medicationforall/dollhouse/doc_image/01.png

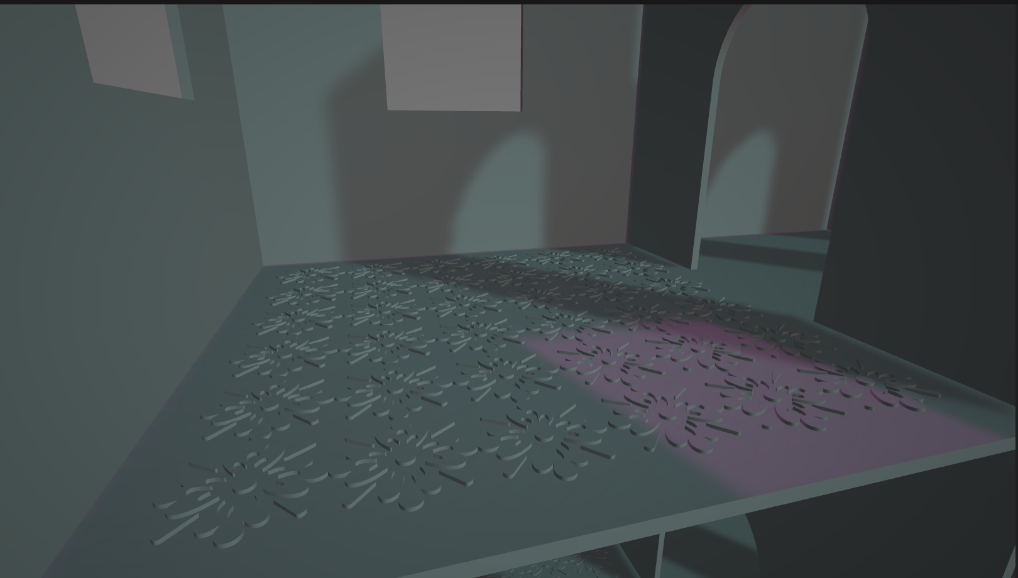
doc_image/01.png
