medicationforall/dollhouse/doc_image/02.png

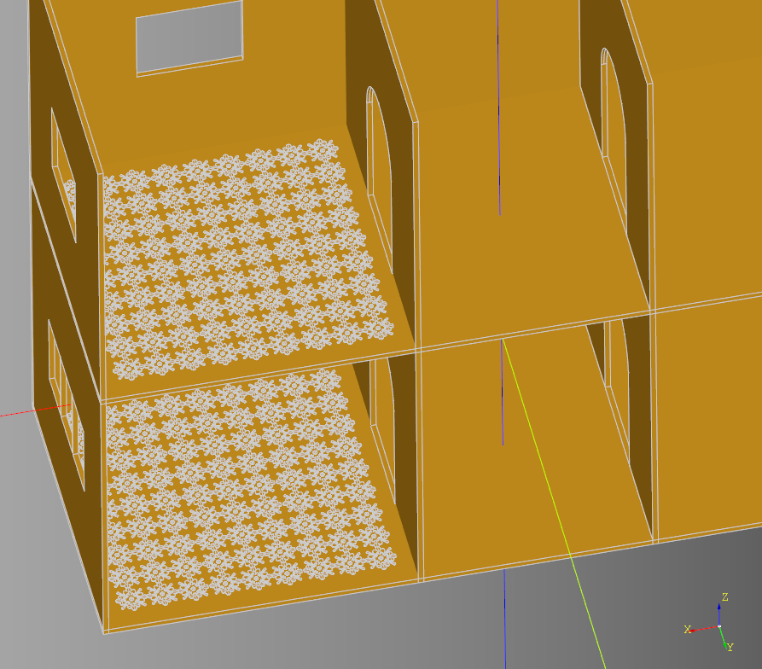
doc_image/02.png
