medicationforall/dollhouse/doc_image/09.png

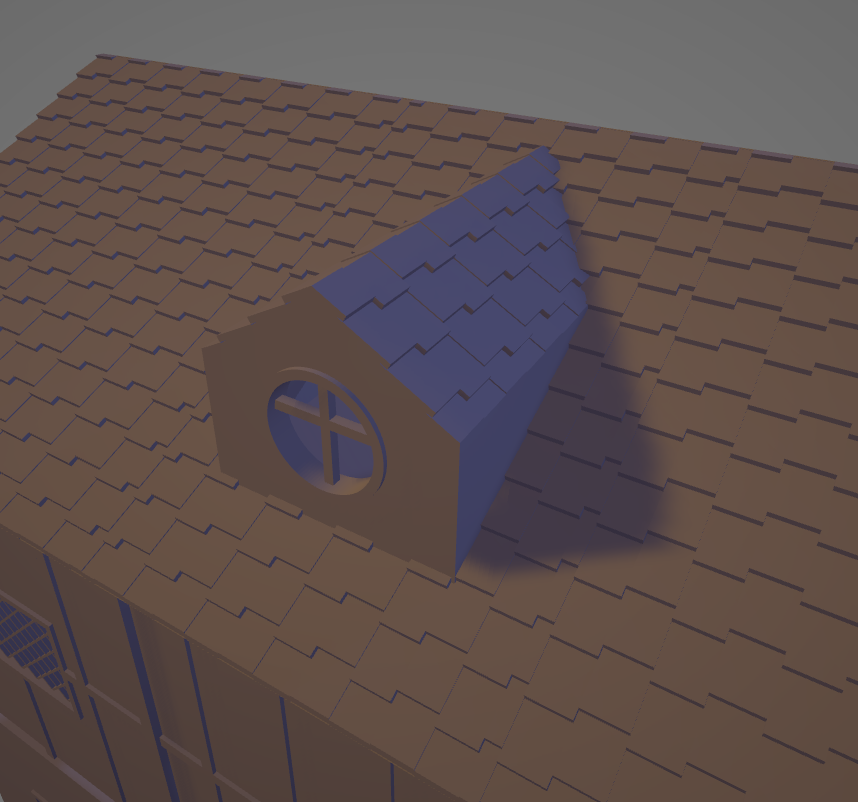
doc_image/09.png
