medicationforall/dollhouse/doc_image/10.png

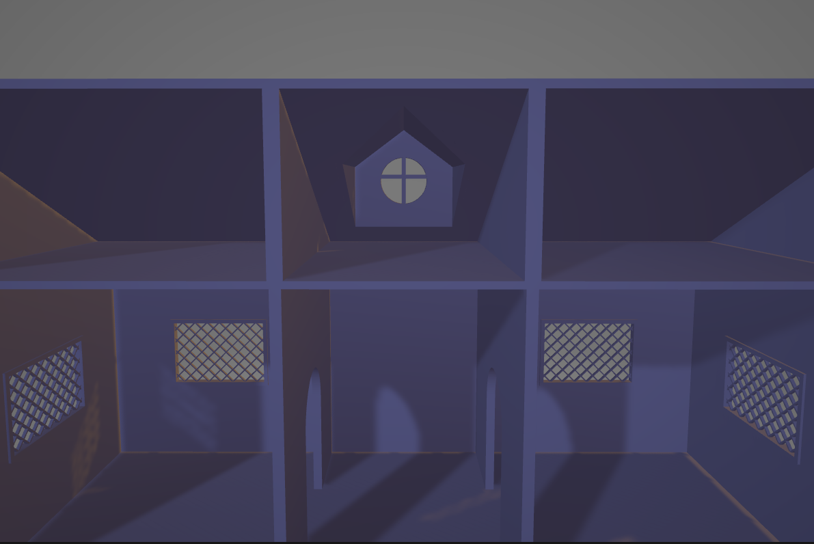
doc_image/10.png
