medicationforall/dollhouse/doc_image/11.png

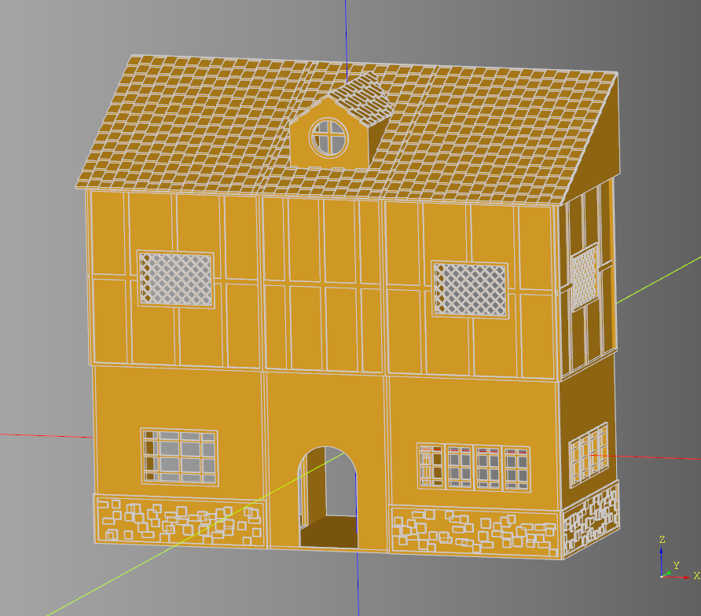
doc_image/11.png
