medicationforall/dollhouse/doc_image/12.png

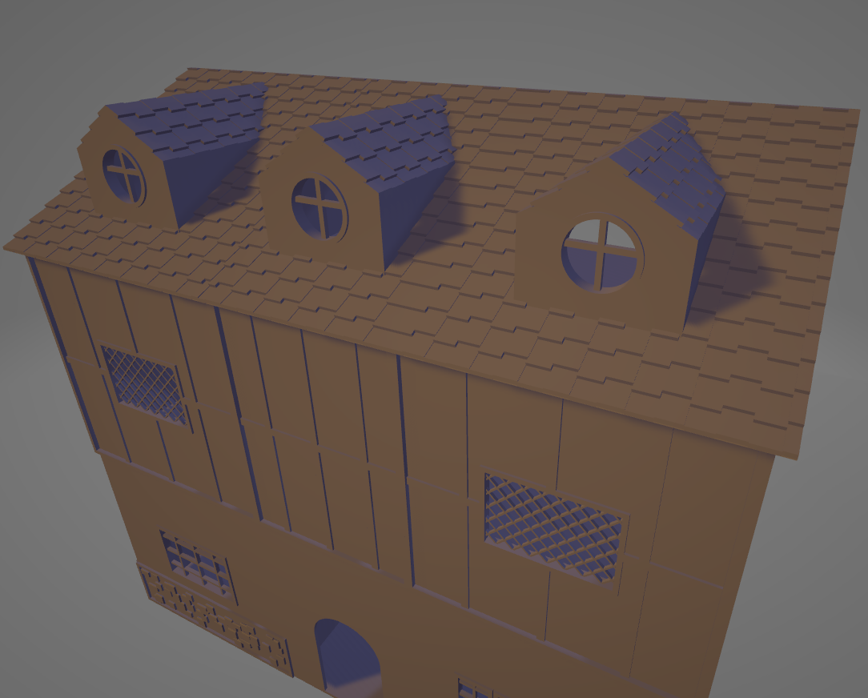
doc_image/12.png
