medicationforall/dollhouse/doc_image/13.png

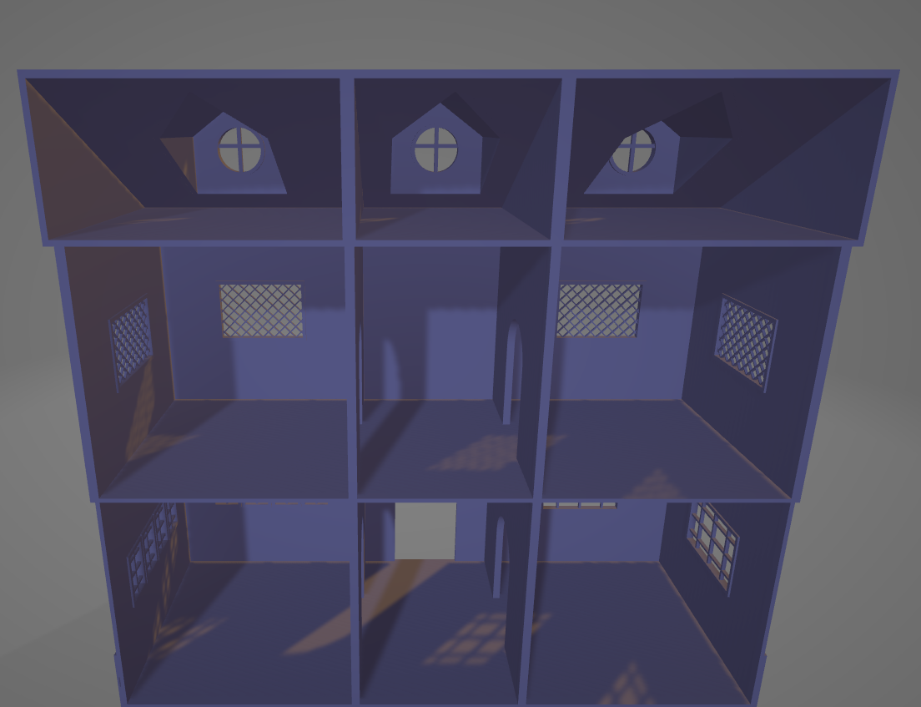
doc_image/13.png
