medicationforall/dollhouse/doc_image/14.png

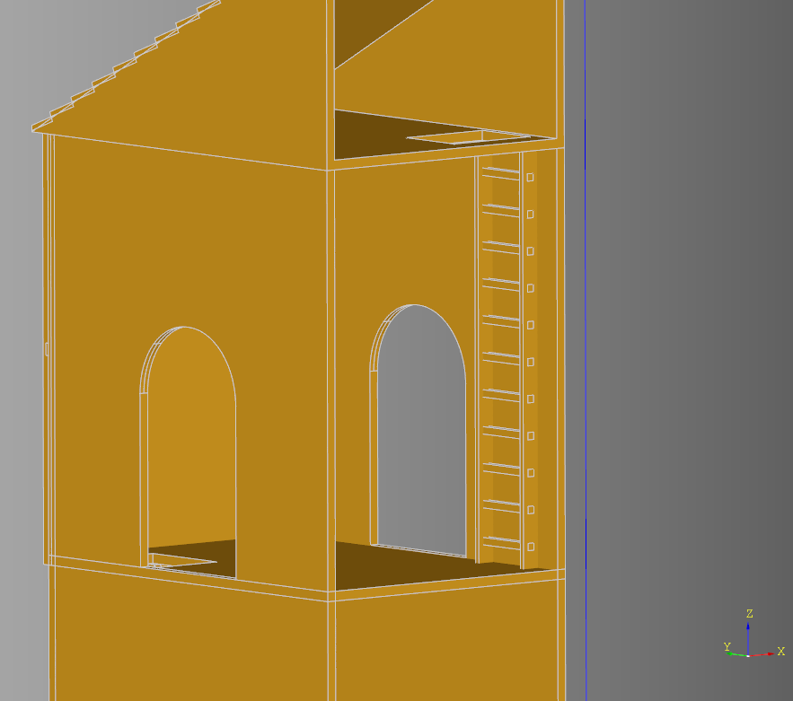
doc_image/14.png
