medicationforall/dollhouse/doc_image/15.png

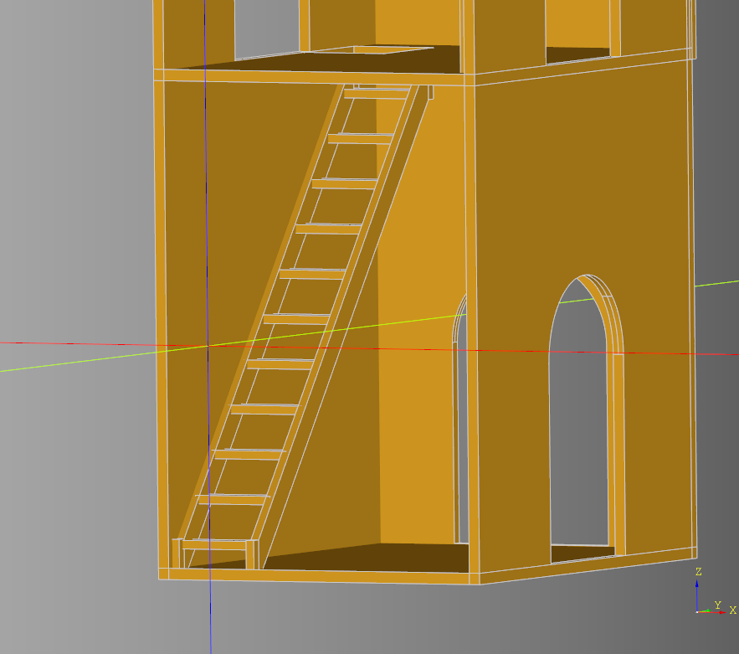
doc_image/15.png
