medicationforall/dollhouse/doc_image/17.png

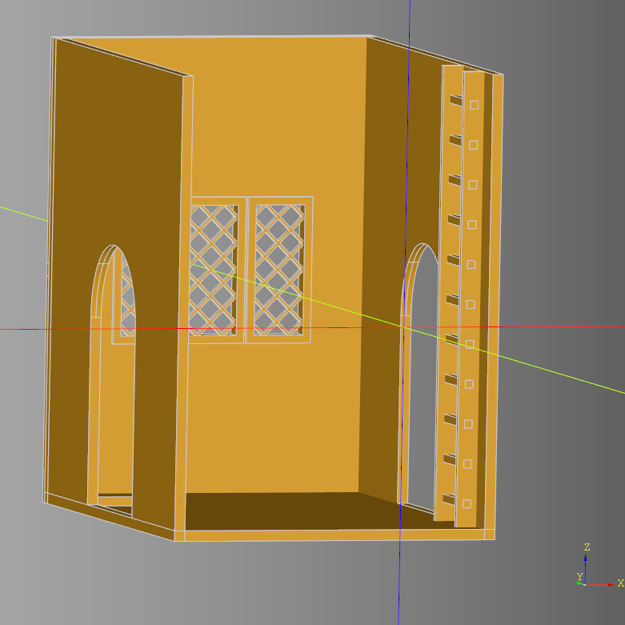
doc_image/17.png
