medicationforall/dollhouse/doc_image/18.png

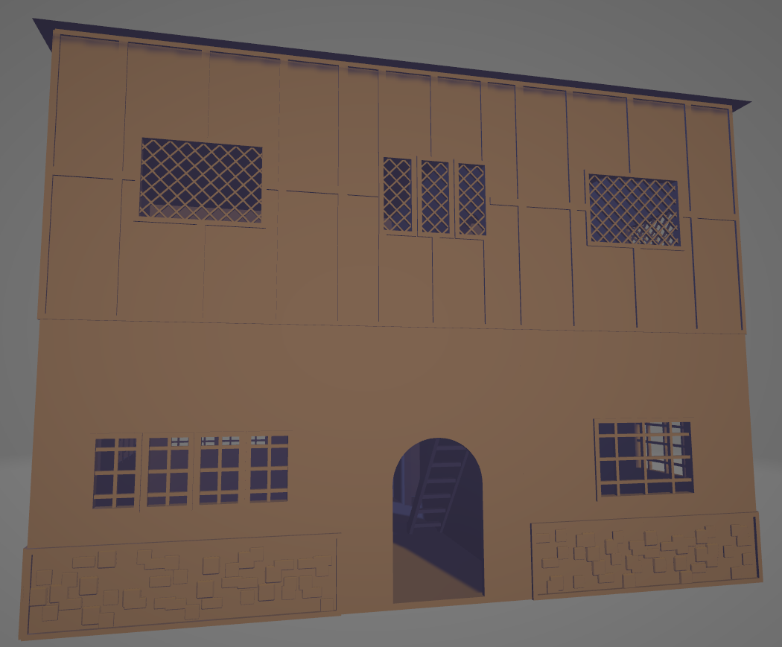
doc_image/18.png
