medicationforall/dollhouse/doc_image/19.png

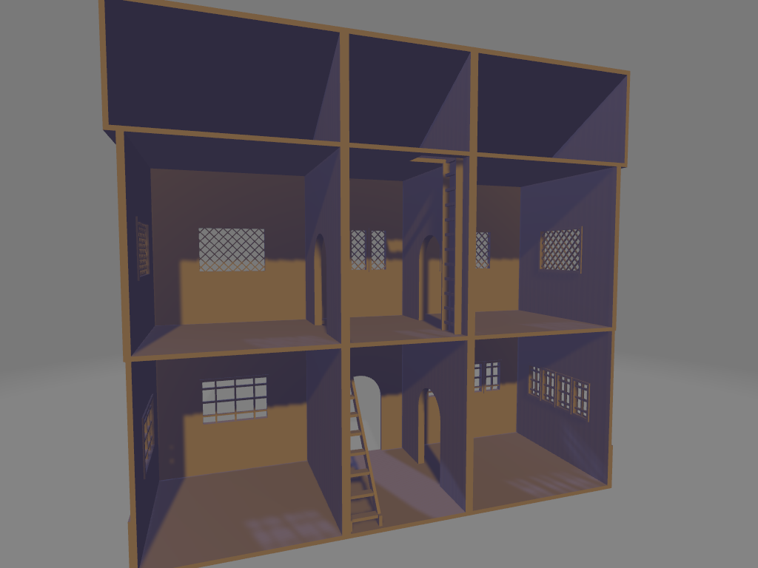
doc_image/19.png
