medicationforall/dollhouse/doc_image/20.png

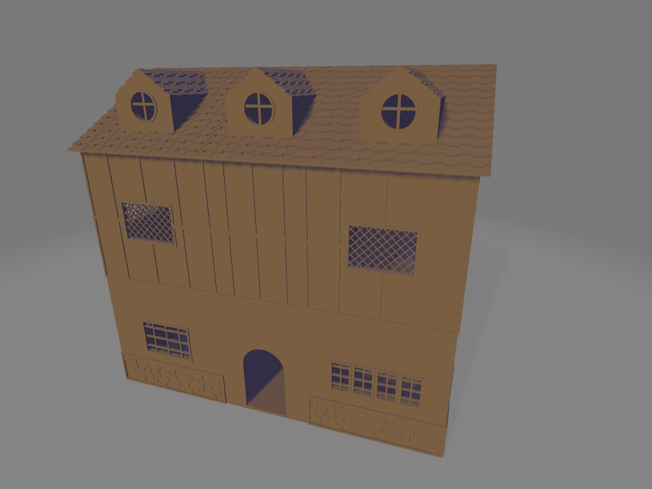
doc_image/20.png
