medicationforall/dollhouse/doc_image/21.png

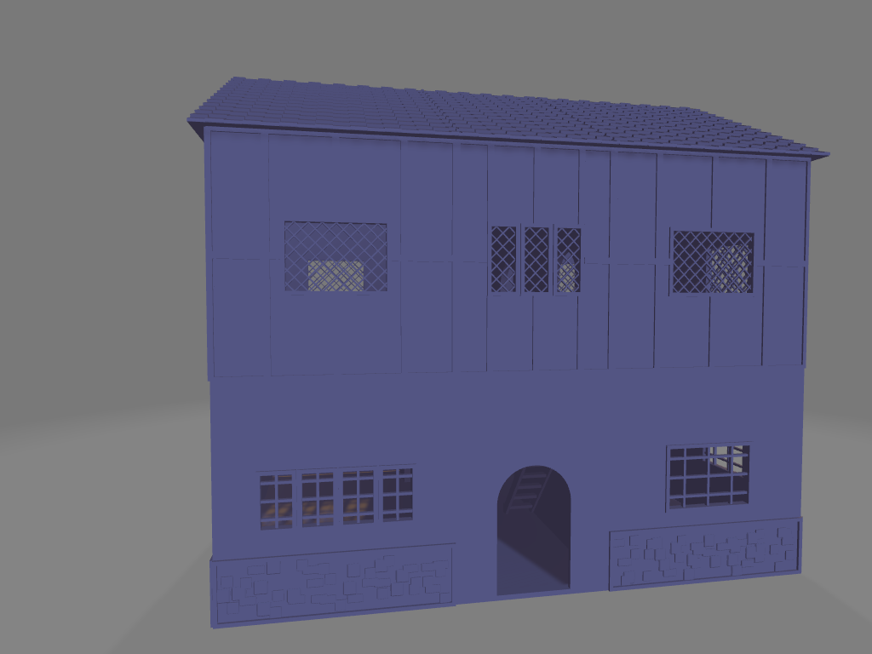
doc_image/21.png
