medicationforall/dollhouse/doc_image/22.png

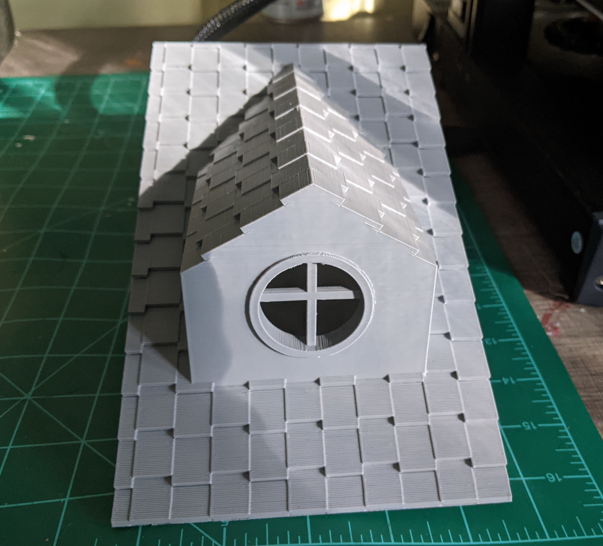
doc_image/22.png
