medicationforall/dollhouse/doc_image/23.png

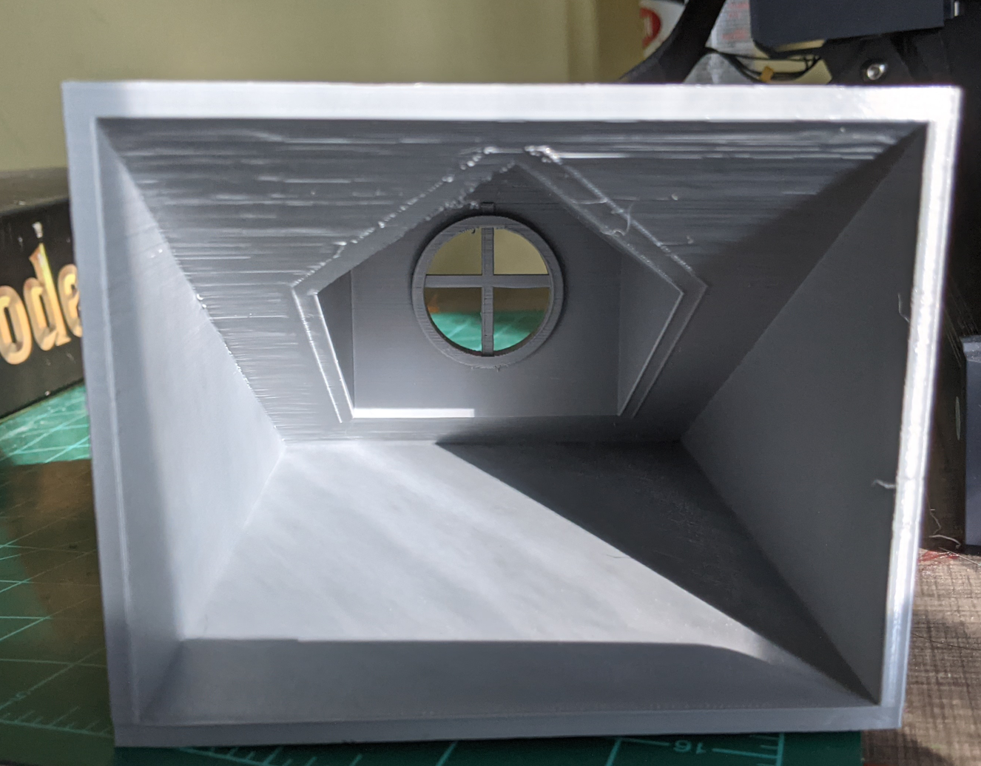
doc_image/23.png
