medicationforall/dollhouse/doc_image/24.png

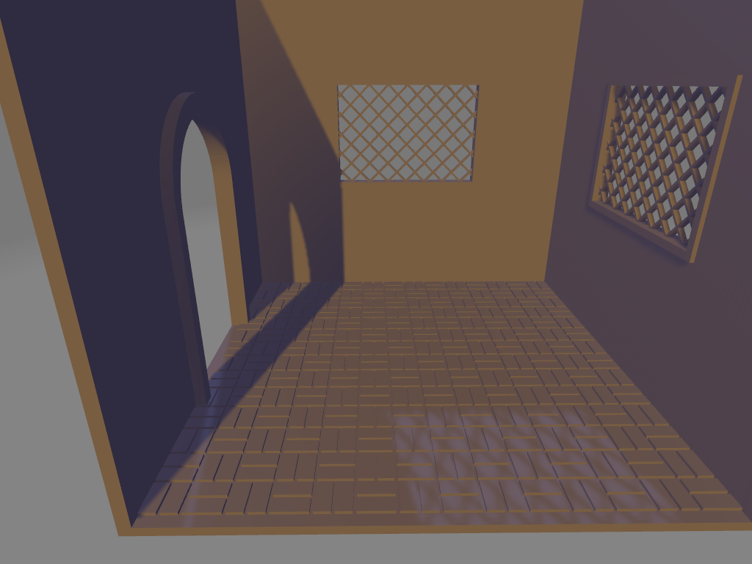
doc_image/24.png
