medicationforall/dollhouse/doc_image/25.png

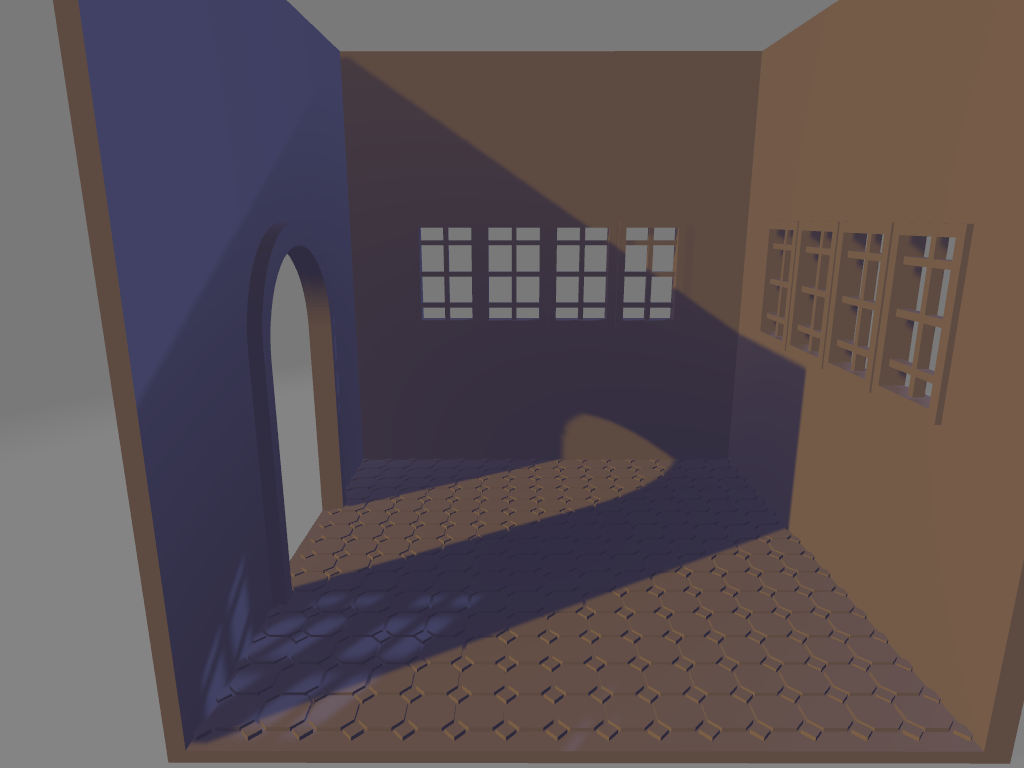
doc_image/25.png
