medicationforall/dollhouse/doc_image/27.png

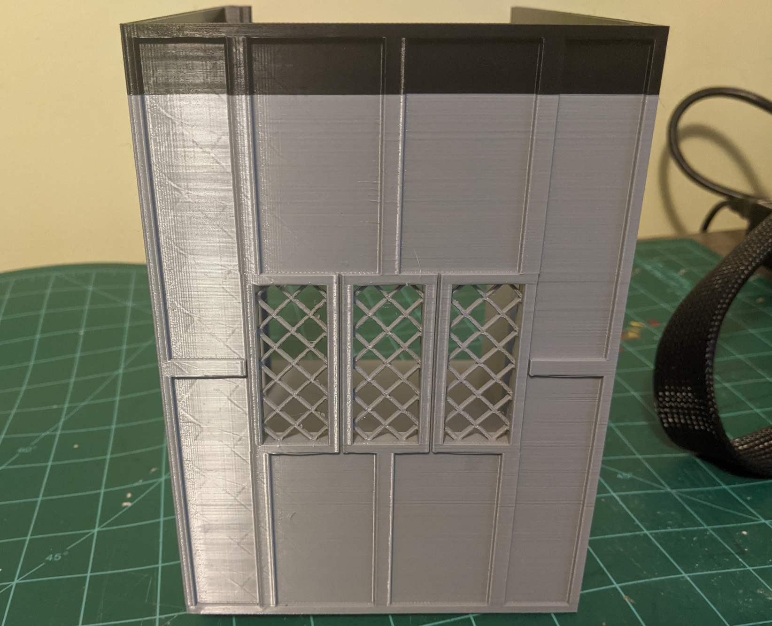
doc_image/27.png
