medicationforall/dollhouse/doc_image/30.png

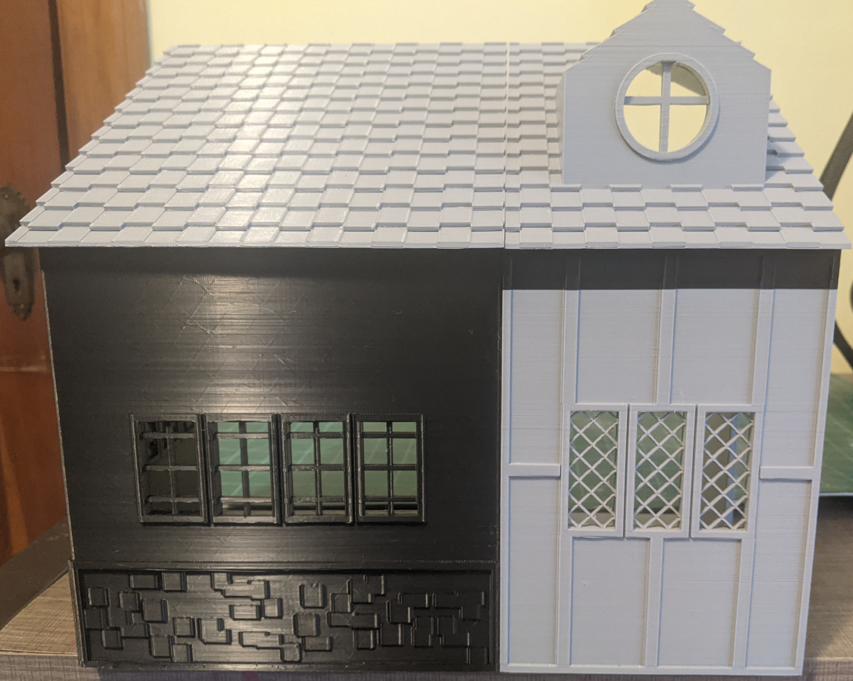
doc_image/30.png
