medicationforall/dollhouse/doc_image/31.png

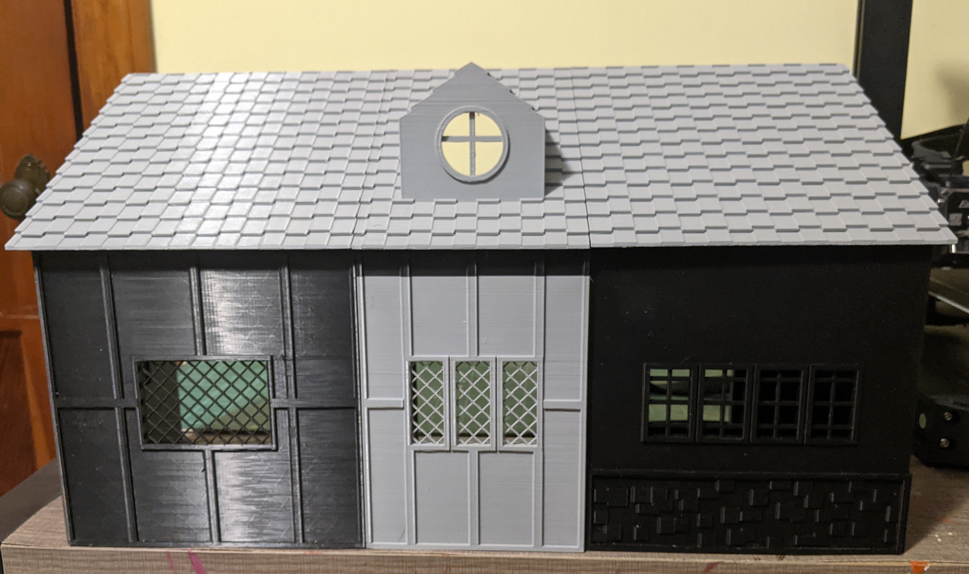
doc_image/31.png
