medicationforall/dollhouse/doc_image/37.png

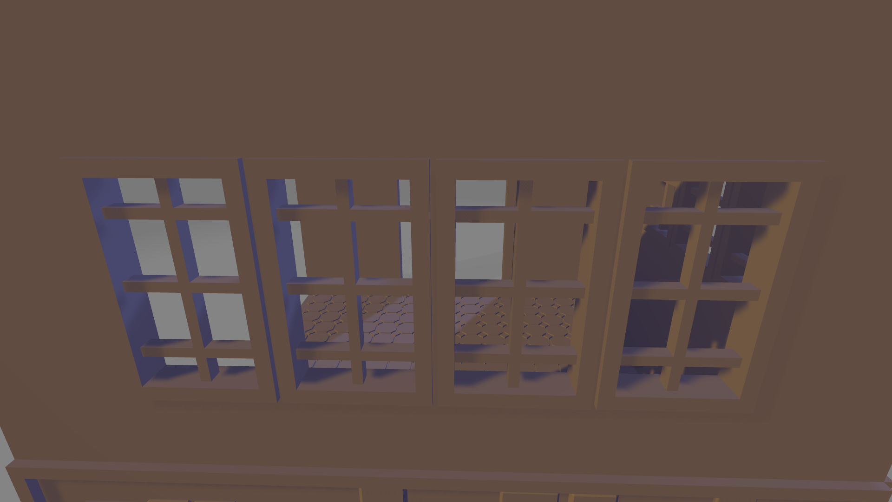
doc_image/37.png
